s100projects/ATX_DC2DC/Docs/IMG_3378.JPG

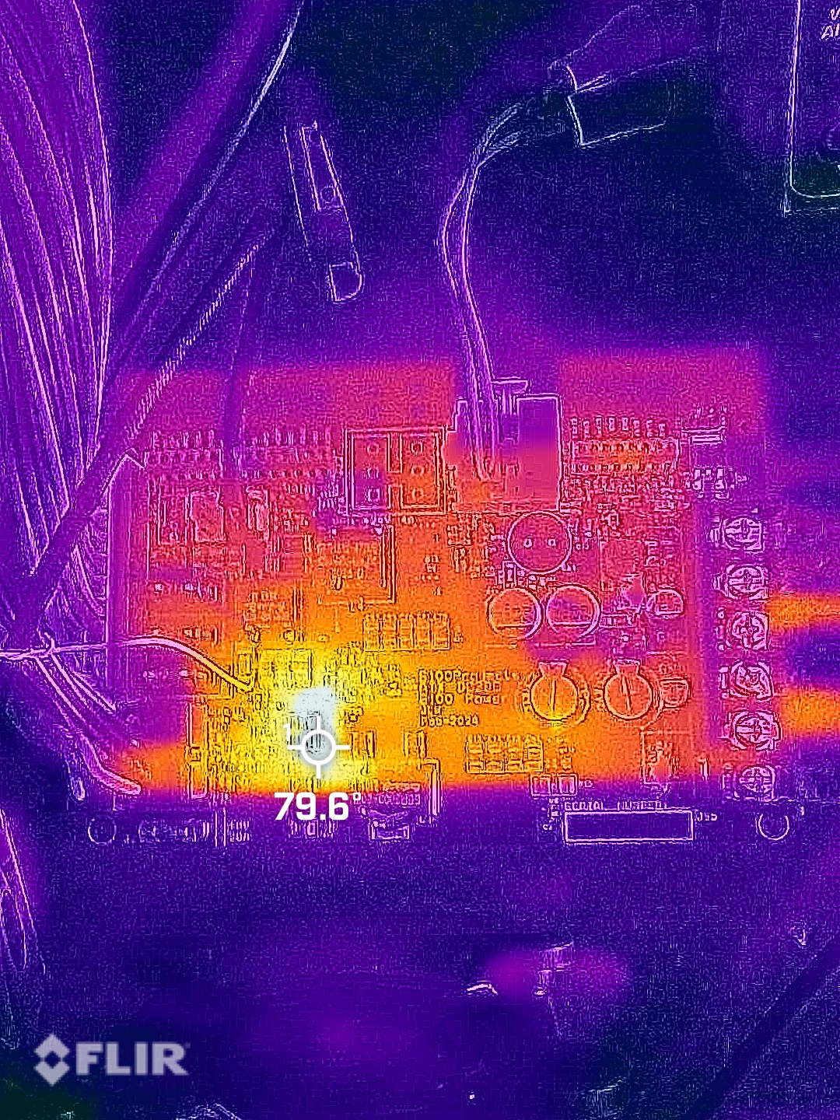
Docs/IMG_3378.JPG
